trwgQ26xxx/FLT_module_reader/firmware/drv/ram_test_data.h

/*
Project name:	FLT/ART/CU1 ROM Reader
Author: 		trwgQ26xxx
Date:			18.01.2025
Target MCUs:	ATmega64/ATmega64L/ATmega64A/ATmega128/ATmega128L/ATmega128A
Compiler:		AVR-GCC version 7.3.0
*/

#ifndef _DRV_RAM_TEST_DATA_H
#define _DRV_RAM_TEST_DATA_H

#include <stdint.h>

#include <avr/pgmspace.h>

//Test data array has to be smaller than 32k due to avr-gcc limitation
#define RAM_TEST_DATA_LENGTH	0x7FF0	//32752b

const uint8_t ram_test_data[RAM_TEST_DATA_LENGTH] PROGMEM = {
	0x10, 0x41, 0x78, 0x72, 0x7C, 0x1D, 0xEE, 0x04, 0xE9, 0x3E, 0x92, 0xC3, 0x91, 0x54, 0x0C, 0x96,
	0x4E, 0xA2, 0x76, 0x56, 0x41, 0xDC, 0xB4, 0x65, 0xFC, 0x19, 0x1E, 0x7A, 0xCF, 0x18, 0xB7, 0x76,
	0x24, 0x7C, 0xAF, 0xC9, 0xB2, 0x2D, 0x05, 0xB3, 0x96, 0x62, 0x54, 0xA9, 0x42, 0xCE, 0x30, 0x33,
	0x92, 0xD9, 0xCD, 0x11, 0xEE, 0x80, 0x7F, 0x57, 0x53, 0x4D, 0x1E, 0xD6, 0x27, 0x78, 0x80, 0x7B,
	0xDF, 0x75, 0x18, 0xA0, 0x64, 0xFF, 0x69, 0x20, 0xE5, 0x52, 0x3E, 0x68, 0x5A, 0xC8, 0x99, 0x6E,
	0x4E, 0x4C, 0x1C, 0xD4, 0x91, 0x86, 0xB0, 0x19, 0x92, 0x78, 0x09, 0xE1, 0x21, 0xFE, 0x4C, 0x05,
	0xA6, 0x6B, 0x82, 0x7C, 0x7C, 0xEB, 0x0A, 0xDD, 0x75, 0x3E, 0x4E, 0x95, 0xE6, 0x3E, 0x42, 0x84,
	0x41, 0x4C, 0xAA, 0x49, 0x0E, 0x55, 0x1C, 0x28, 0x1C, 0x70, 0xD5, 0x5A, 0x0A, 0xF0, 0x67, 0x98,
	0xCA, 0x45, 0xC4, 0xE6, 0x02, 0xB4, 0xF9, 0x54, 0x6C, 0x85, 0x41, 0x9C, 0xBB, 0xE9, 0x54, 0xDF,
	0x5C, 0x73, 0x6F, 0x09, 0x23, 0xE6, 0x9C, 0xB4, 0x0C, 0xD7, 0xD2, 0x3A, 0x01, 0xDD, 0xD5, 0xE9,
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
	0x33, 0xA1, 0x76, 0x01, 0x81, 0xB7, 0x4C, 0x4C, 0x87, 0x8D, 0x05, 0xDC, 0x8E, 0xE8, 0xA6, 0x3A,
	0xA3, 0x8F, 0xB2, 0x9D, 0x51, 0x11, 0x2C, 0xA3, 0x41, 0x1D, 0x4D, 0x07, 0xD3, 0x38, 0xDE, 0x18,
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
};

#endif
